atfinke/RX/R1/images/Config for V5.jpeg

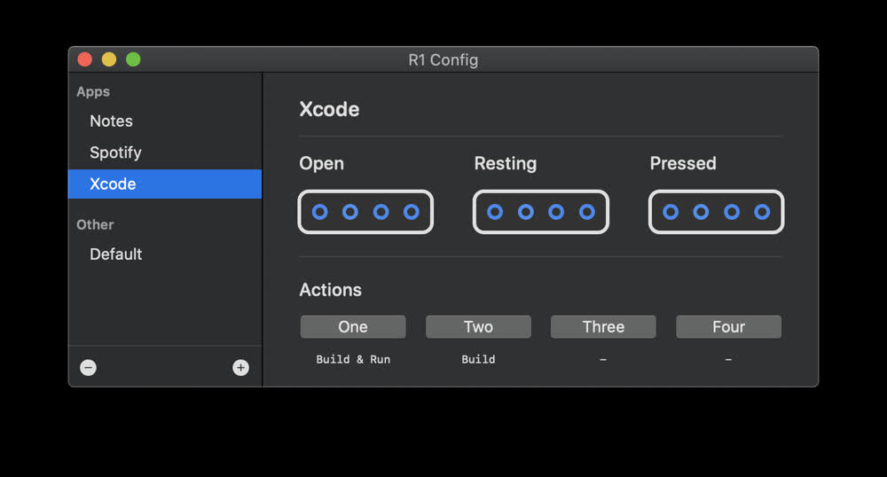
R1/images/Config for V5.jpeg
