atfinke/RX/R1/images/play.jpeg

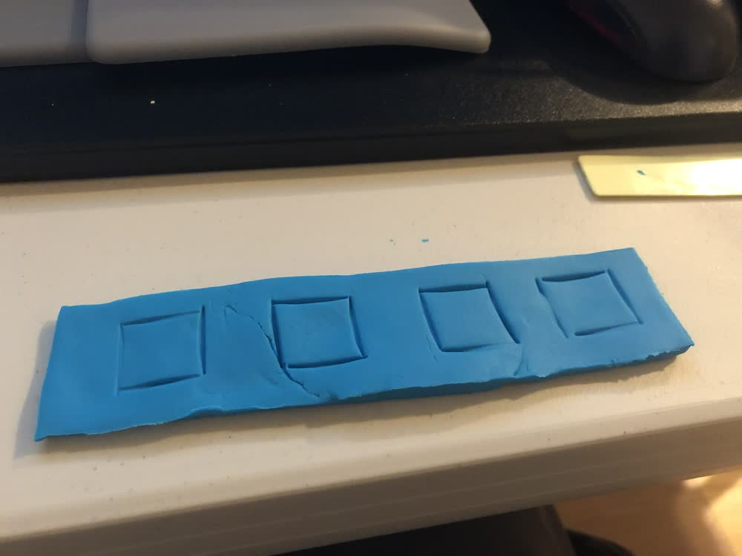
R1/images/play.jpeg
