atfinke/RX/R1/images/Proto V10.jpeg

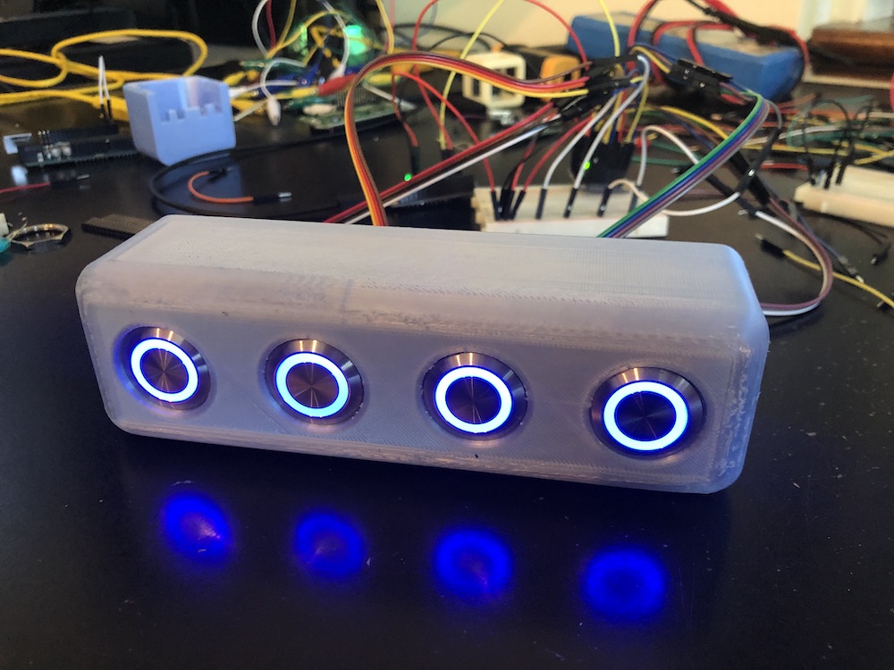
R1/images/Proto V10.jpeg
