atfinke/RX/R1/images/Proto V13 First Power On.jpeg

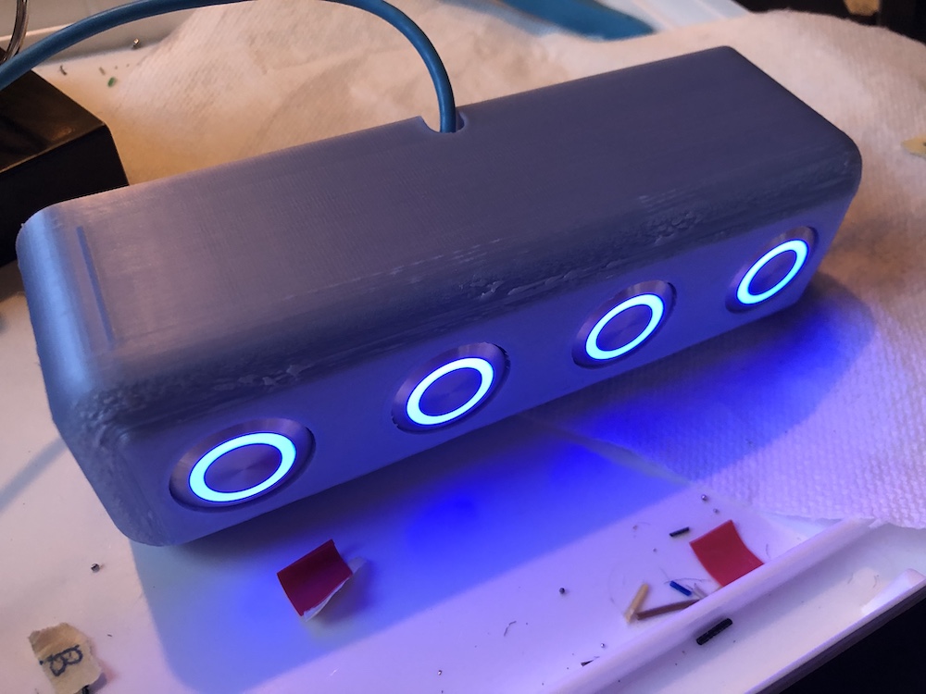
R1/images/Proto V13 First Power On.jpeg
