atfinke/RX/R1/images/Proto V13 Slightly Open.jpeg

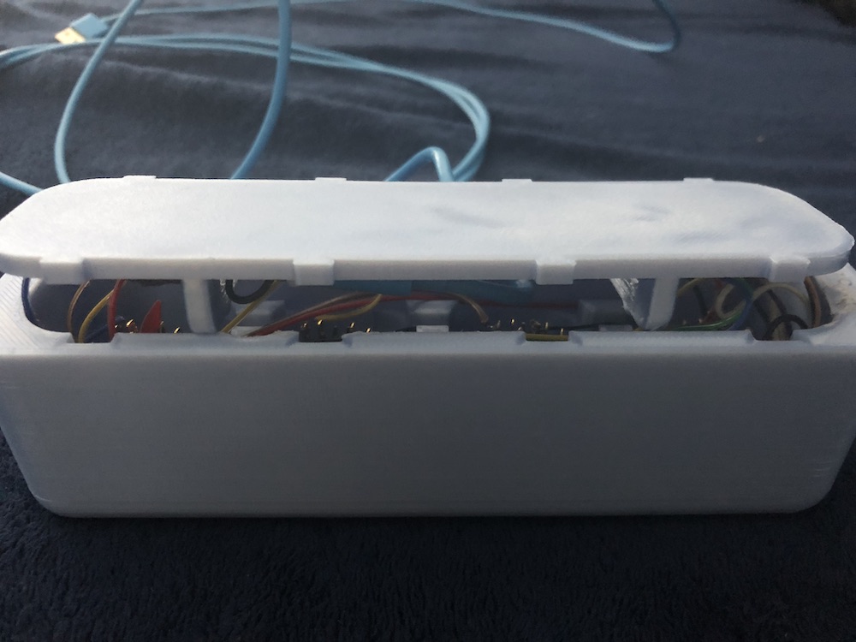
R1/images/Proto V13 Slightly Open.jpeg
