atfinke/RX/R1/images/R1 CNC Off.jpg

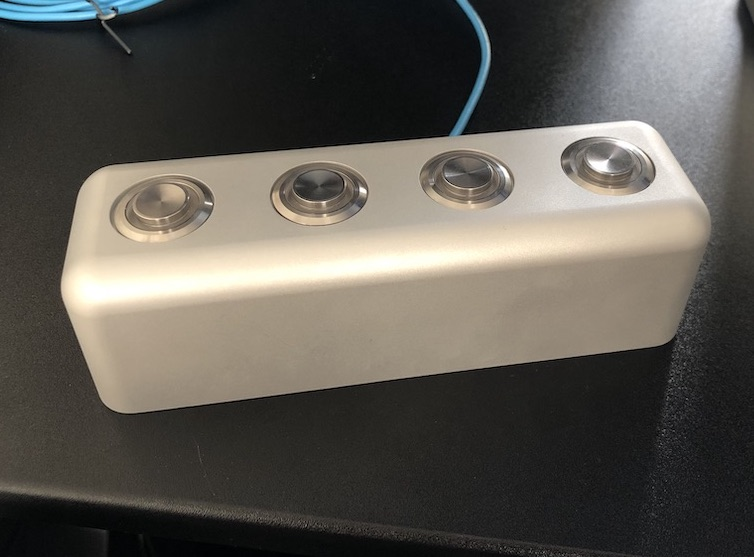
R1/images/R1 CNC Off.jpg
