atfinke/RX/R1/images/R1 CNC On.jpg

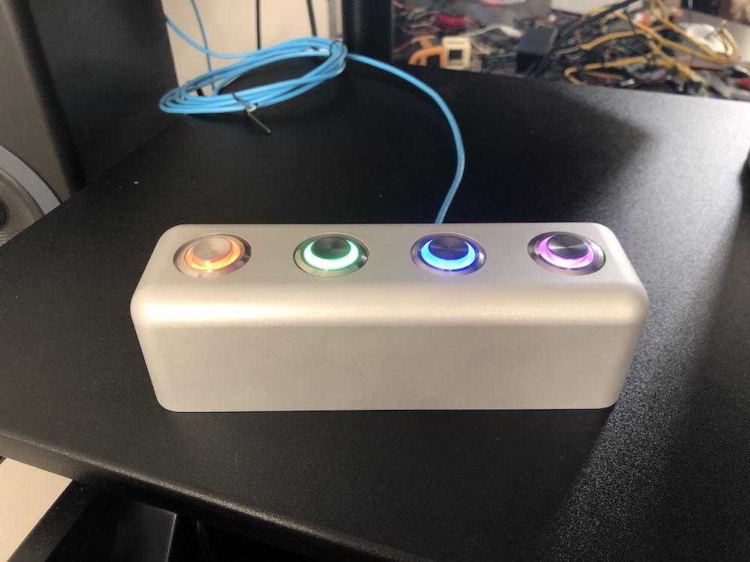
R1/images/R1 CNC On.jpg
