atfinke/RX/R1/images/R1 Finals.jpg

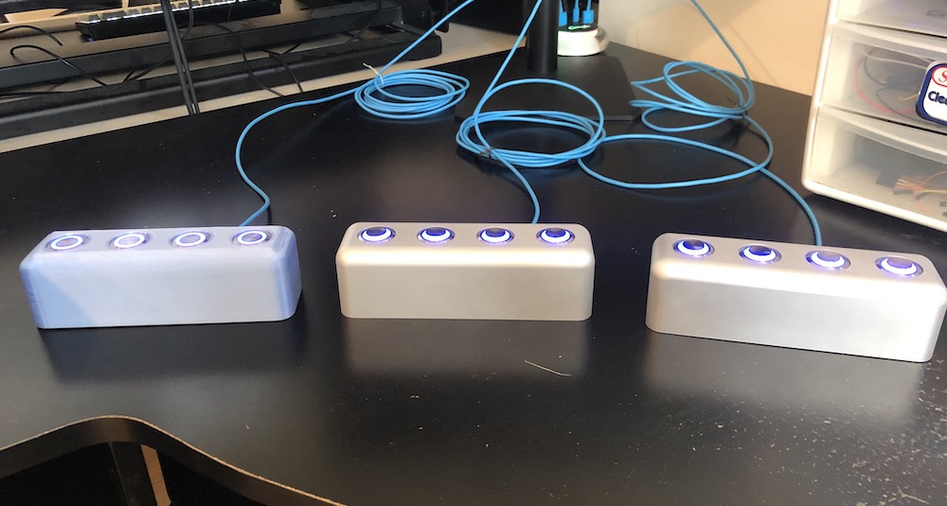
R1/images/R1 Finals.jpg
