atfinke/RX/RD/images/RD Boards.jpg

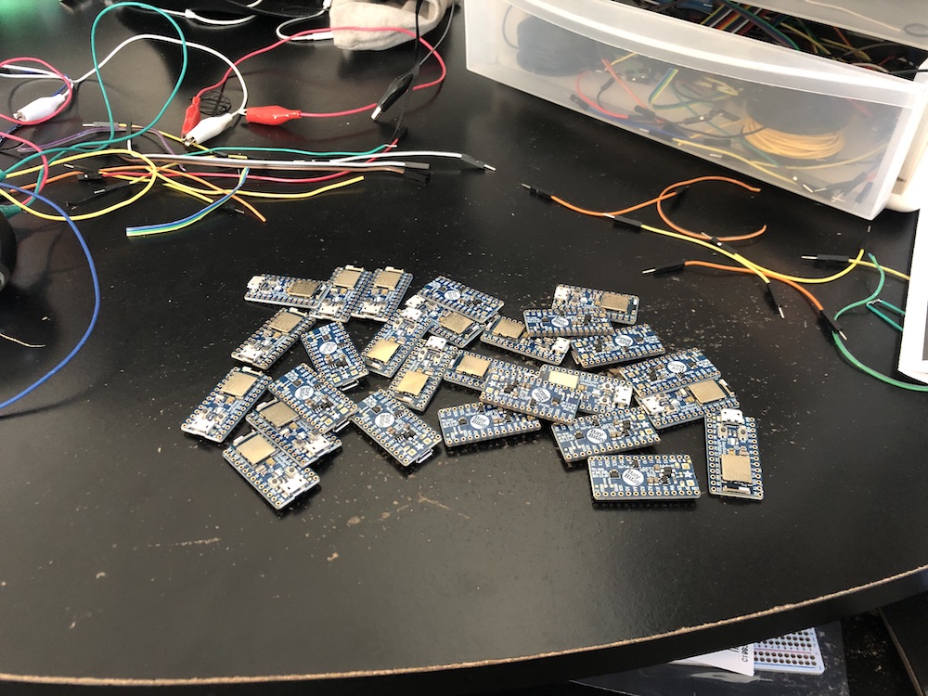
RD/images/RD Boards.jpg
