atfinke/RX/RD/images/RD Hatching.jpeg

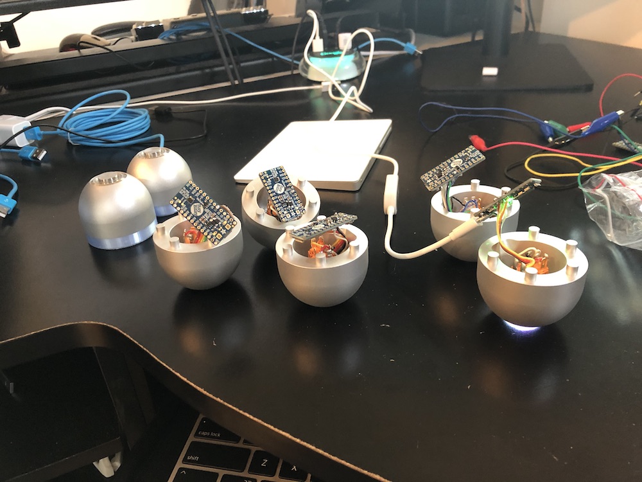
RD/images/RD Hatching.jpeg
