atfinke/RX/RM/images/base + top.jpeg

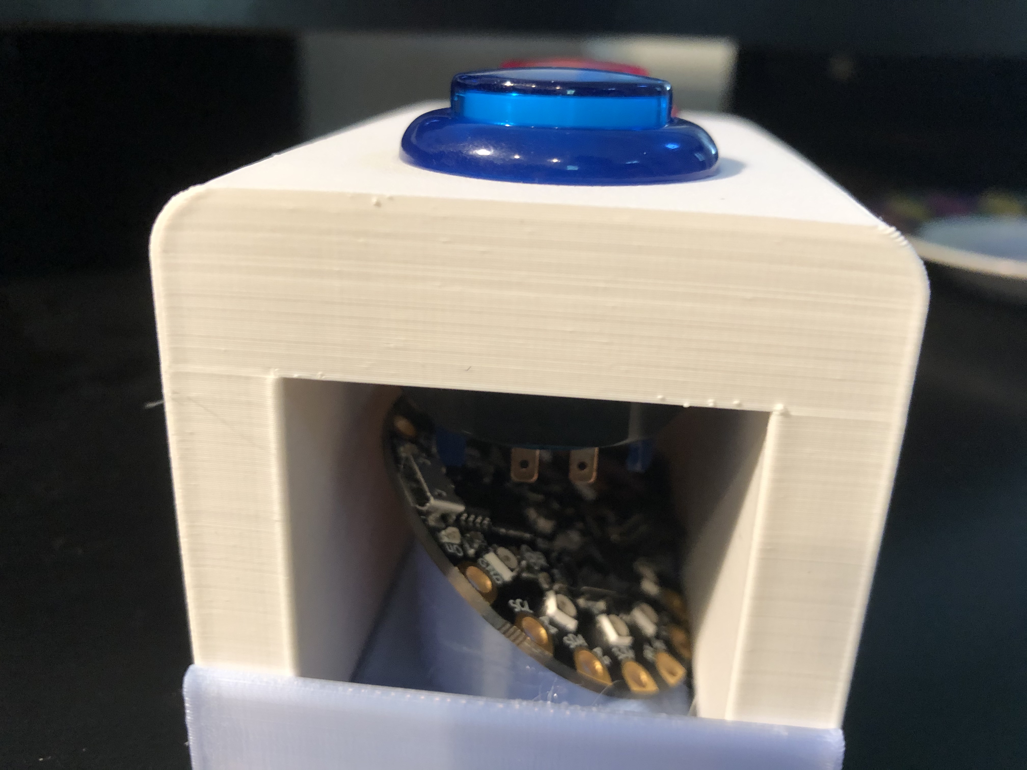
RM/images/base + top.jpeg
