atfinke/RX/RM/images/base.jpeg

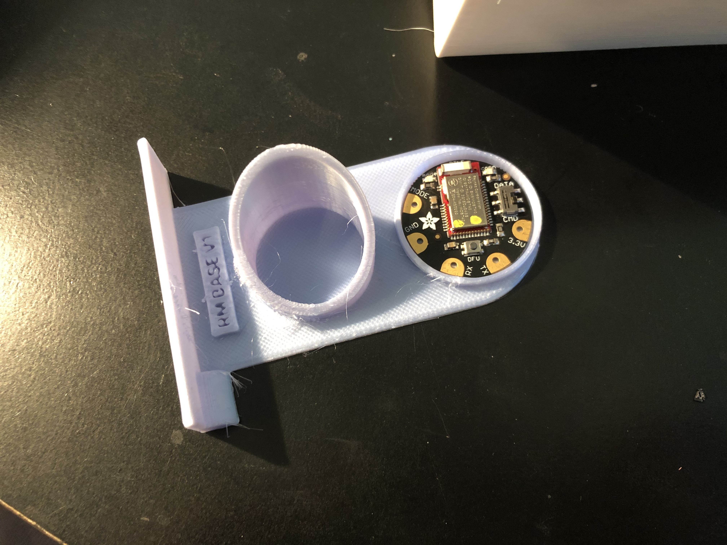
RM/images/base.jpeg
