atfinke/RX/RD/cad/RD V8 T.stl

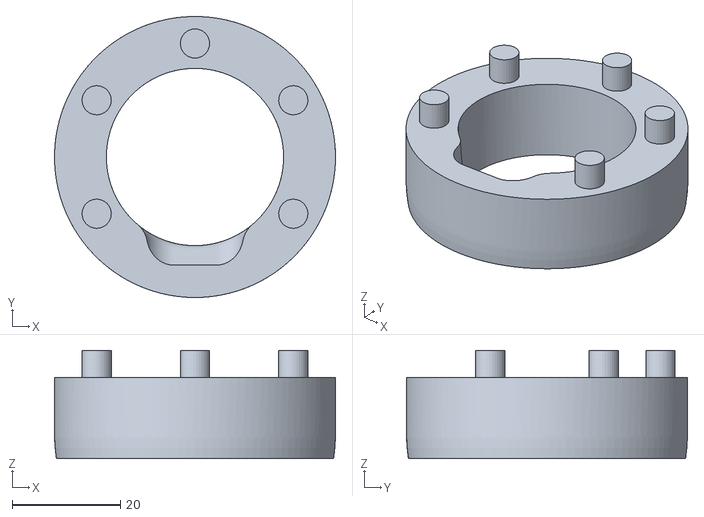
[picture p34: CAD file, 2020-09-12]
RD/cad/RD V8 T.stl
52.0 x 52.0 x 20.0
