atfinke/RX/R1/cad/R1 Proto V13.stl

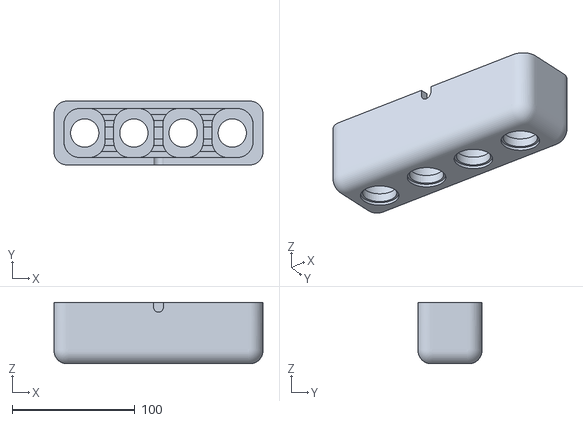
[picture p35: CAD file, 2020-06-29]
R1/cad/R1 Proto V13.stl
170.0 x 52.0 x 50.0
