atfinke/RX/R1/images/Proto V10 Wiring.jpeg

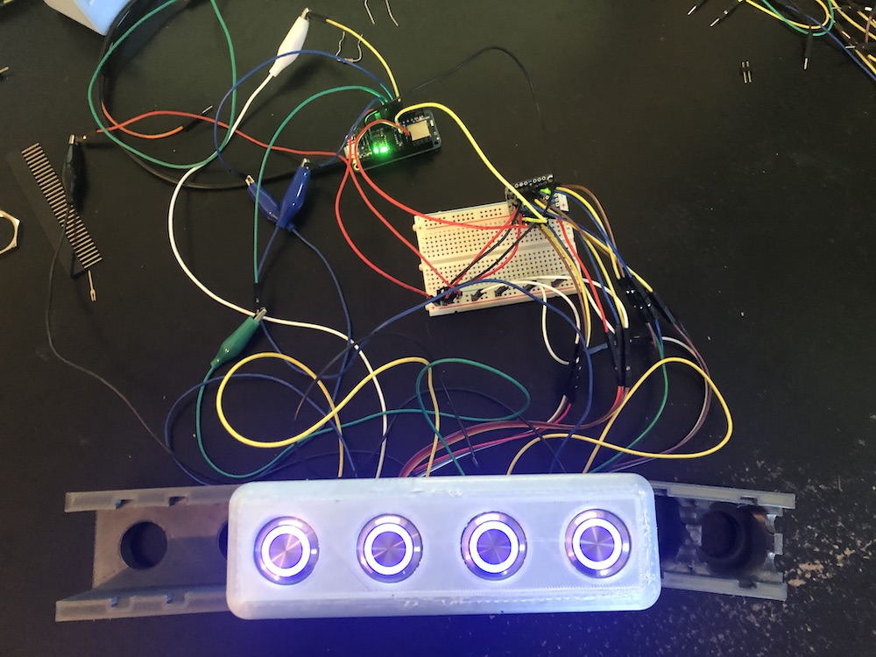
R1/images/Proto V10 Wiring.jpeg
