atfinke/RX/R1/images/Proto V13 Partial Wiring.jpeg

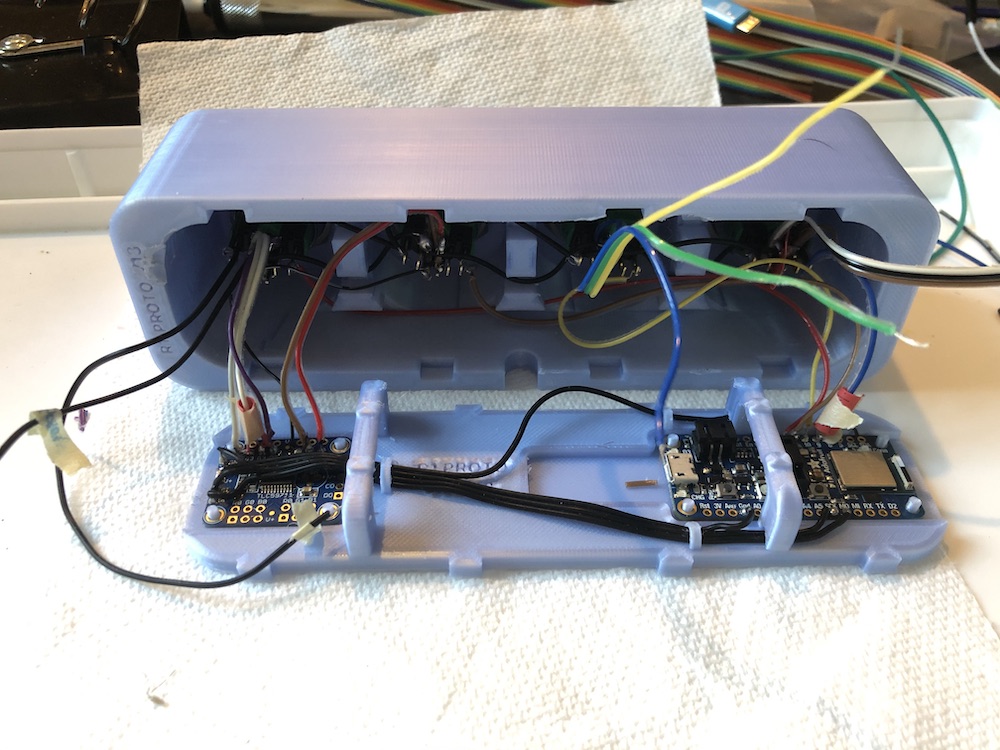
R1/images/Proto V13 Partial Wiring.jpeg
