atfinke/RX/RM/images/post solder.jpeg

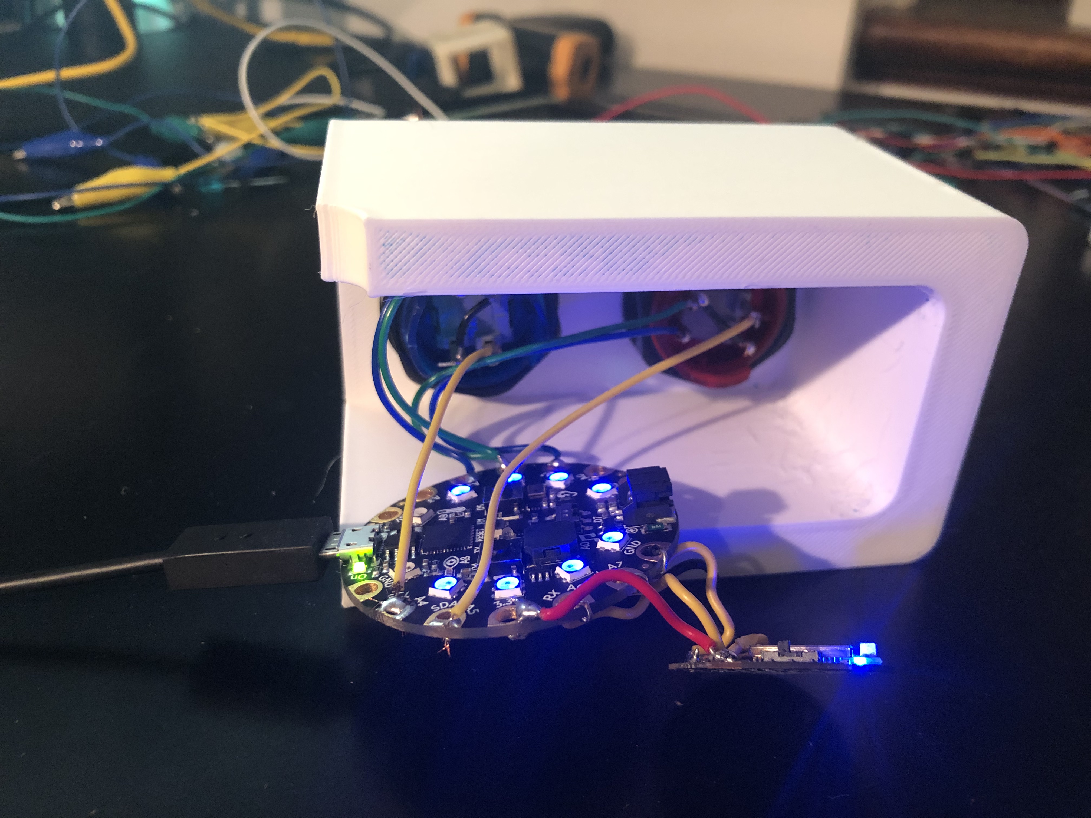
RM/images/post solder.jpeg
