atfinke/RX/R1/images/Proto V1 Test.jpeg

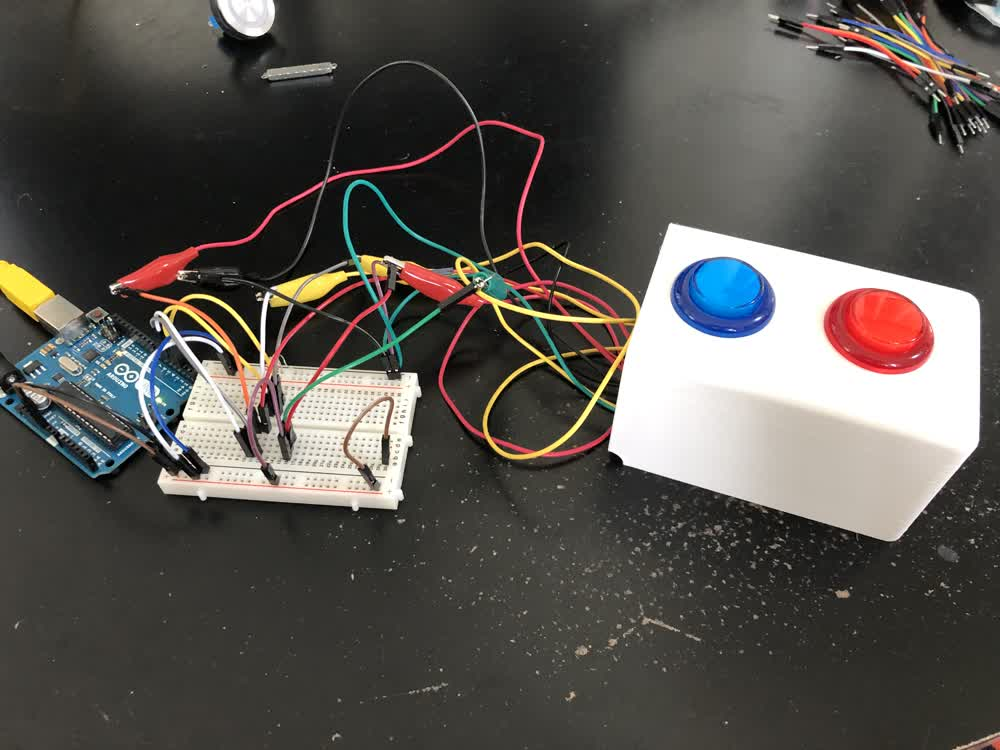
R1/images/Proto V1 Test.jpeg
