atfinke/RX/R1/images/pwm test.jpeg

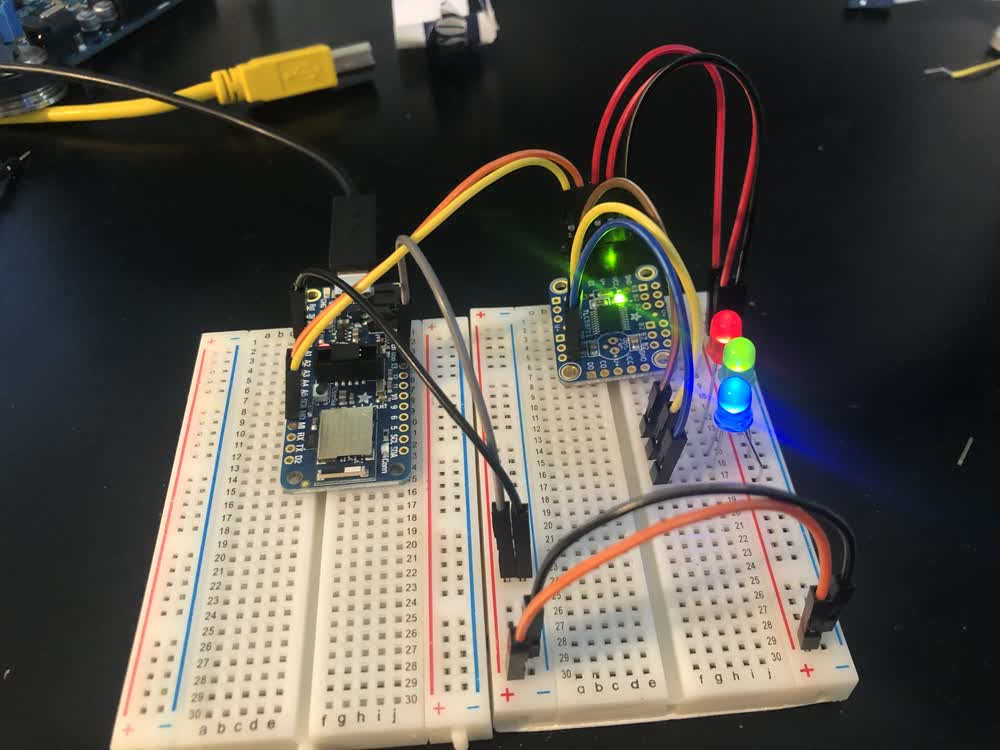
R1/images/pwm test.jpeg
